hexeguitar/TGX4/hardware/img/TGX4codecModule_mount.jpg

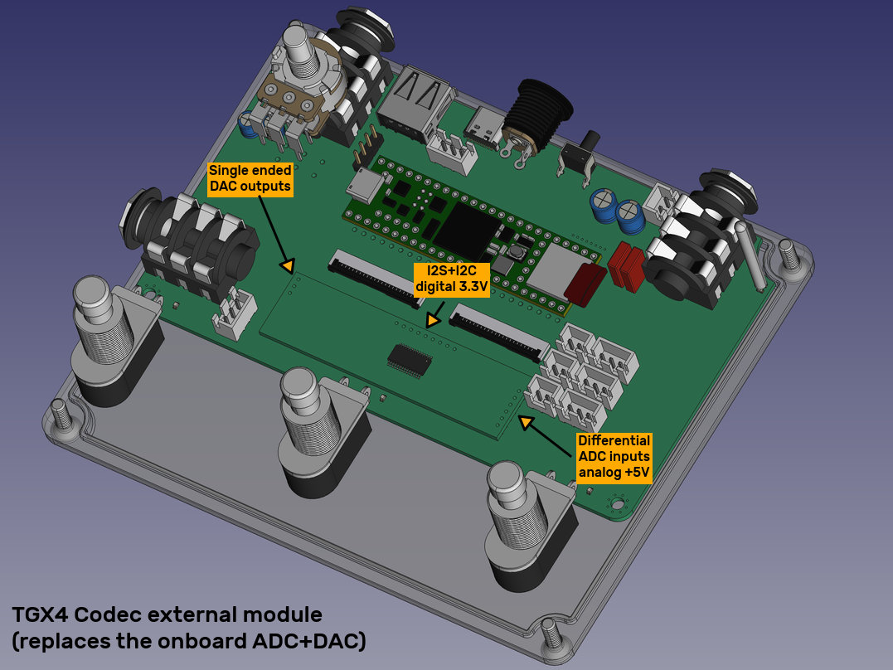
hardware/img/TGX4codecModule_mount.jpg
