hexeguitar/TGX4/hardware/KiCad_proj/MainBoard/AK5552_I2S.png

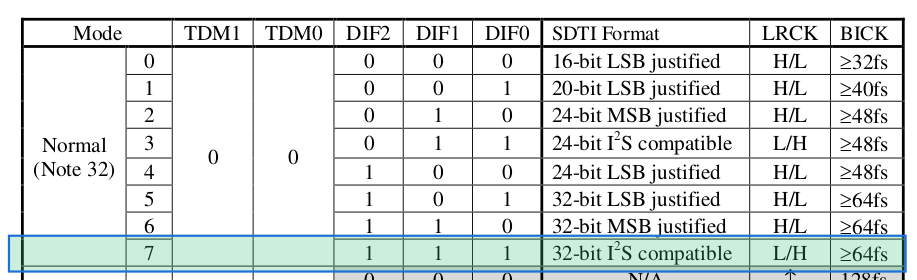
hardware/KiCad_proj/MainBoard/AK5552_I2S.png
