hexeguitar/TGX4/hardware/KiCad_proj/FrontPanel/TGX4_Panel.kicad_sch

## KiCad design hardware/KiCad_proj/FrontPanel/TGX4_Panel.kicad_sch (2024-12-13)

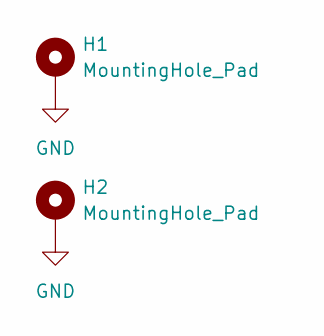
[picture p39: schematic TGX4_Panel.kicad_sch]

Parts:
H1, H2: MountingHole_Pad; MountingHole_3.2mm_M3_DIN965_Pad

Connections:
GND: H1.1, H2.1
