hexeguitar/TGX4/hardware/KiCad_proj/MainBoard/ADC_sch.kicad_sch

## KiCad design hardware/KiCad_proj/MainBoard/ADC_sch.kicad_sch (2024-07-30)

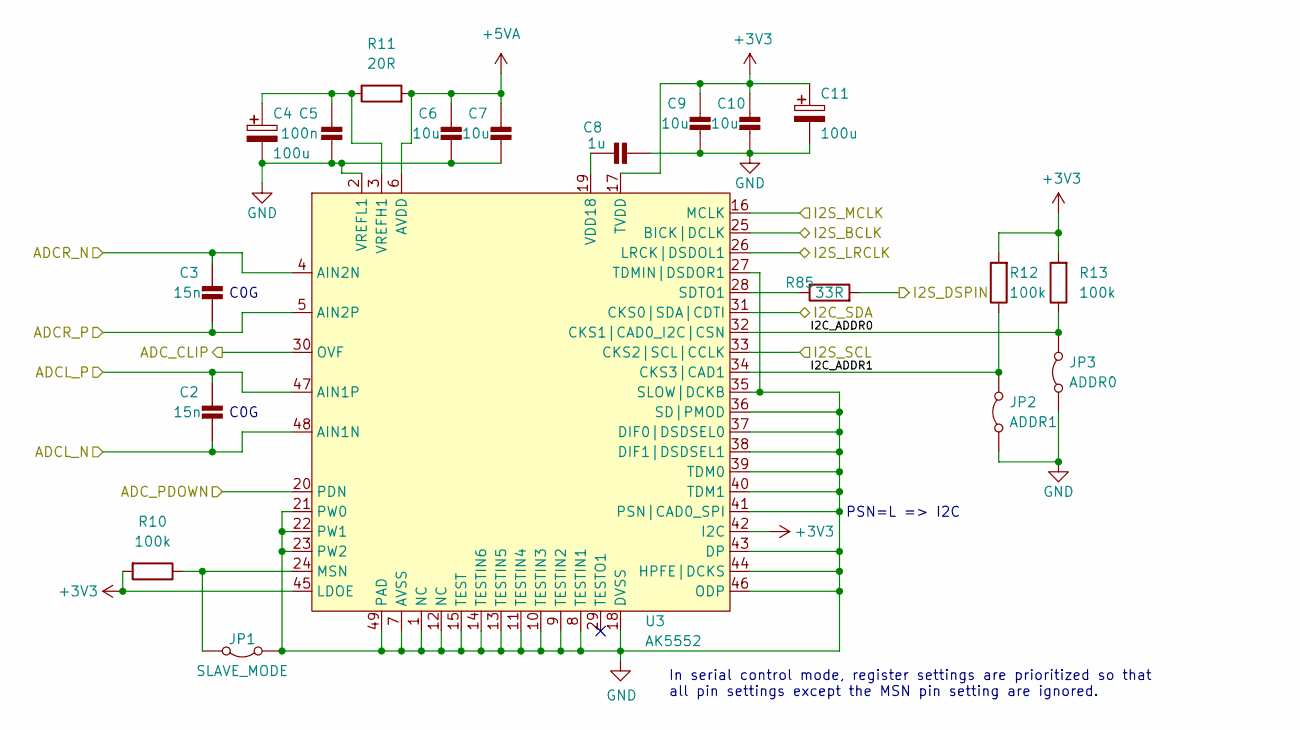
[picture p40: schematic ADC_sch.kicad_sch]

Parts:
C2, C3: 15n; Hx_C_0805_2012Metric
C4, C11: 100u; CP_EIA-6032-28_Kemet-C
C5: 100n; Hx_C_0805_2012Metric
C6, C7, C9, C10: 10u; Hx_C_0805_2012Metric
C8: 1u; Hx_C_0805_2012Metric
JP1: SLAVE_MODE; PCB_jumper_2_closed
JP2: ADDR1; PCB_jumper_2_closed
JP3: ADDR0; PCB_jumper_2_closed
R10, R12, R13: 100k; Hx_R_0805_2012Metric
R11: 20R; Hx_R_0805_2012Metric
R85: 33R; Hx_R_0805_2012Metric
U3: AK5552; QFN-48-1EP_7x7mm_P0.5mm_EP5.15x5.15mm

Connections:
+3V3: C9.1, C10.1, C11.1, R10.2, R12.2, R13.2, U3.17 (TVDD), U3.42 (I2C), U3.45 (LDOE)
+5VA: C6.1, C7.1, R11.2, U3.6 (AVDD)
ADCL_N: C2.2, U3.48 (AIN1N)
ADCL_P: C2.1, U3.47 (AIN1P)
ADCR_N: C3.1, U3.4 (AIN2N)
ADCR_P: C3.2, U3.5 (AIN2P)
ADC_CLIP: U3.30 (OVF)
ADC_PDOWN: U3.20 (PDN)
GND: C4.2, C5.2, C6.2, C7.2, C8.2, C9.2, C10.2, C11.2, JP1.1 (A), JP2.1 (A), JP3.1 (A), U3.1 (NC), U3.2 (VREFL1), U3.7 (AVSS), U3.8 (TESTIN1), U3.9 (TESTIN2), U3.10 (TESTIN3), U3.11 (TESTIN4), U3.12 (NC), U3.13 (TESTIN5), U3.14 (TESTIN6), U3.15 (TEST), U3.18 (DVSS), U3.21 (PW0), U3.22 (PW1), U3.23 (PW2), U3.27 (TDMIN|DSDOR1), U3.35 (SLOW|DCKB), U3.36 (SD|PMOD), U3.37 (DIF0|DSDSEL0), U3.38 (DIF1|DSDSEL1), U3.39 (TDM0), U3.40 (TDM1), U3.41 (PSN|CAD0_SPI), U3.43 (DP), U3.44 (HPFE|DCKS), U3.46 (ODP), U3.49 (PAD)
I2C_ADDR0: JP3.2 (B), R13.1, U3.32 (CKS1|CAD0_I2C|CSN)
I2C_ADDR1: JP2.2 (B), R12.1, U3.34 (CKS3|CAD1)
I2C_SDA: U3.31 (CKS0|SDA|CDTI)
I2S_BCLK: U3.25 (BICK|DCLK)
I2S_DSPIN: R85.2
I2S_LRCLK: U3.26 (LRCK|DSDOL1)
I2S_MCLK: U3.16 (MCLK)
I2S_SCL: U3.33 (CKS2|SCL|CCLK)
unnamed: C4.1, C5.1, R11.1, U3.3 (VREFH1)
unnamed: C8.1, U3.19 (VDD18)
unnamed: JP1.2 (B), R10.1, U3.24 (MSN)
unnamed: R85.1, U3.28 (SDTO1)

Notes on the sheet:
C0G
PSN=L => I2C
In serial control mode, register settings are prioritized so that all pin settings except the MSN pin setting are ignored.
