hexeguitar/TGX4/hardware/KiCad_proj/MainBoard/Audio_Input.kicad_sch

## KiCad design hardware/KiCad_proj/MainBoard/Audio_Input.kicad_sch (2024-07-30)

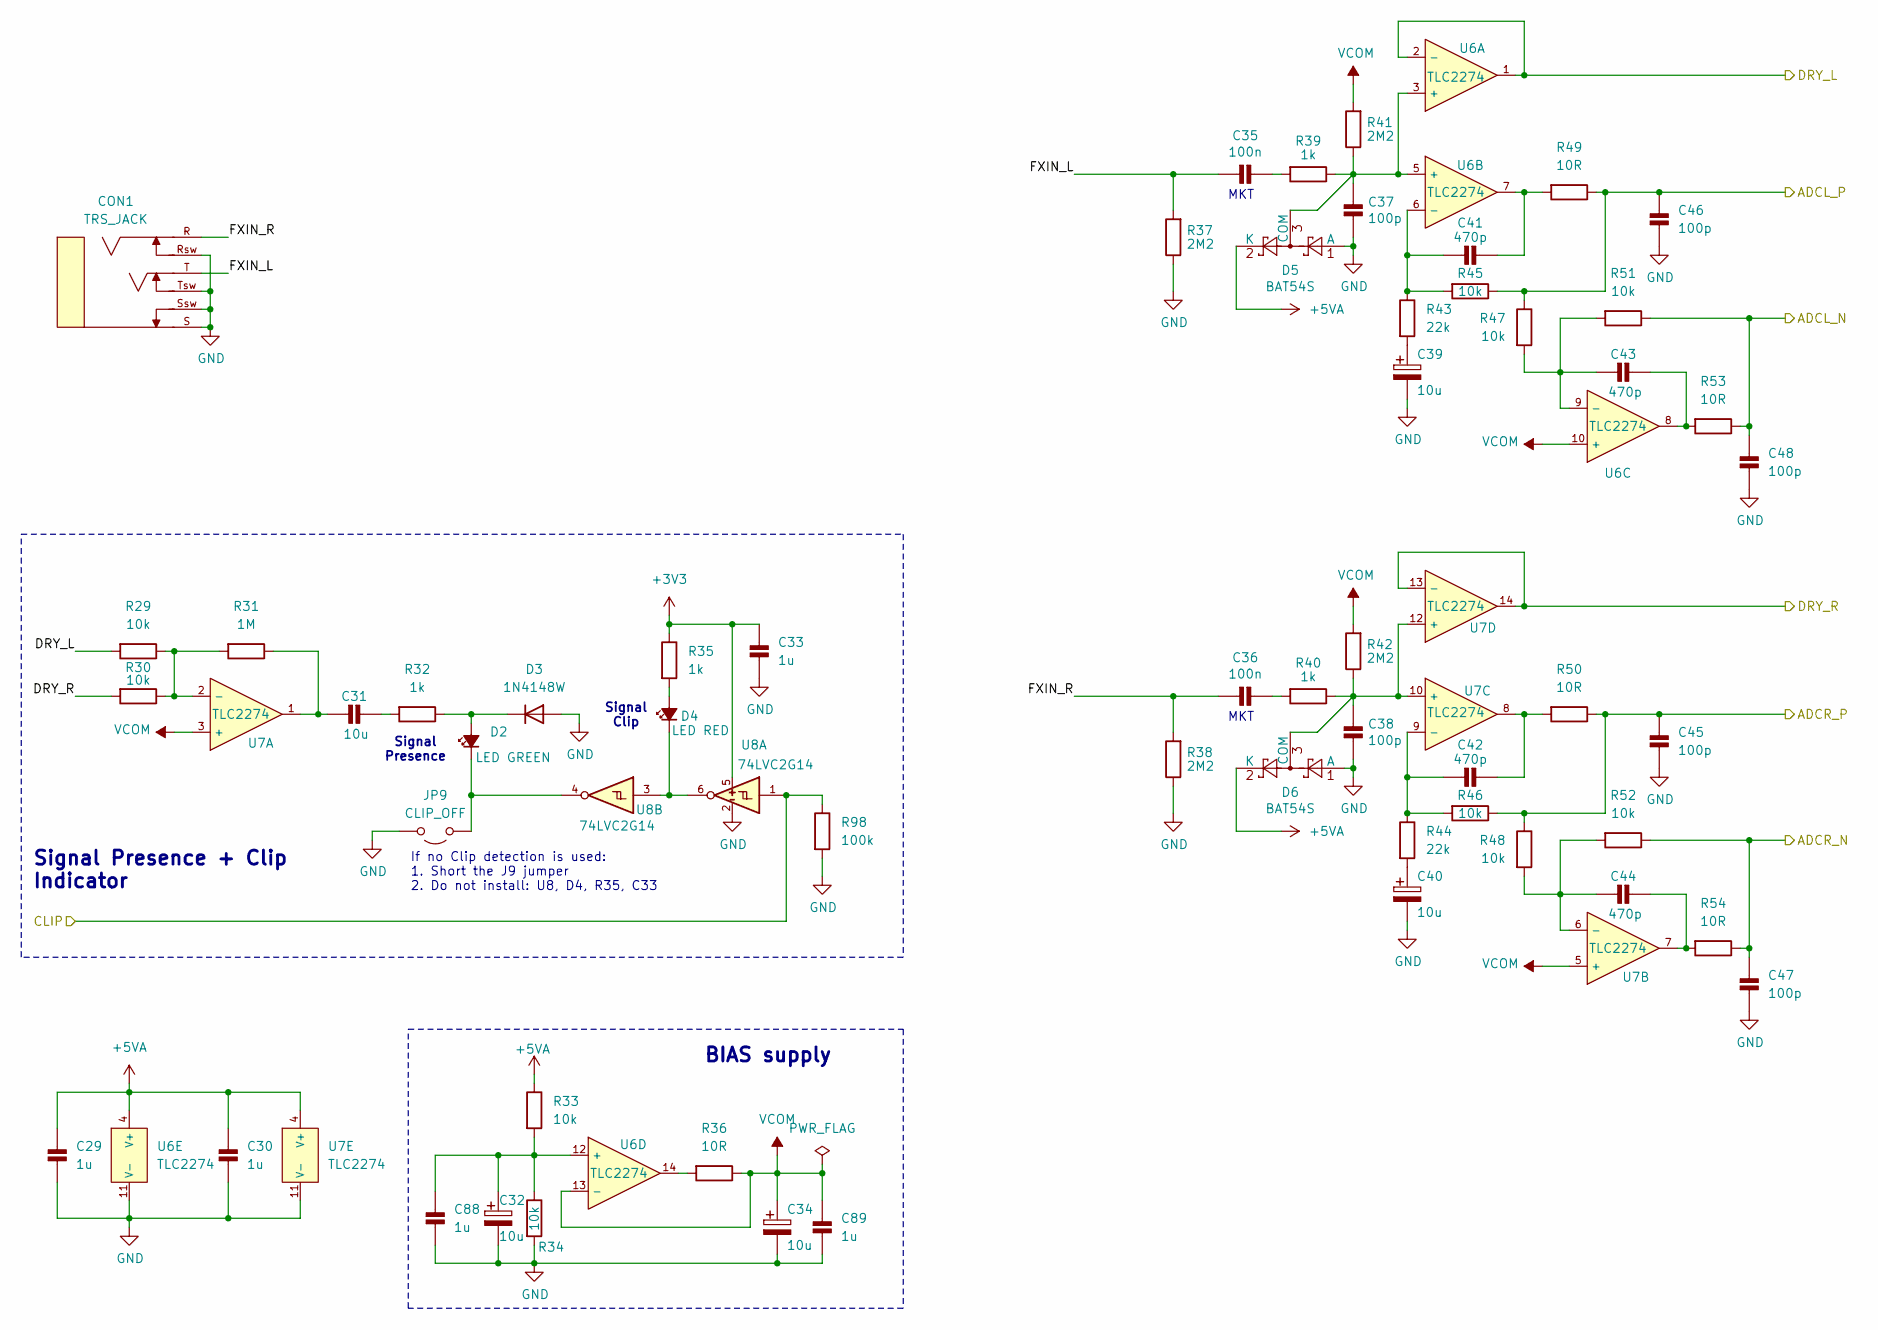
[picture p41: schematic Audio_Input.kicad_sch]

Parts:
C29, C30, C33, C88, C89: 1u; Hx_C_0805_2012Metric
C31: 10u; Hx_C_0805_2012Metric
C32, C34, C39, C40: 10u; CP_EIA-3216-18_Kemet-A
C35, C36: 100n; C_Rect_L7.0mm_W2.5mm_P5.00mm
C37, C38, C45, C46, C47, C48: 100p; Hx_C_0805_2012Metric
C41, C42, C43, C44: 470p; Hx_C_0805_2012Metric
CON1: TRS_JACK; NMJ6HCD2_TRSjack_smallPads
D2: LED GREEN; LED_0603_1608Metric
D3: 1N4148W; D_SOD-123
D4: LED RED; LED_0603_1608Metric
D5, D6: BAT54S; SOT-23
JP9: CLIP_OFF; PCB_jumper_2
R29, R30, R33, R34, R45, R46, R47, R48, R51, R52: 10k; Hx_R_0805_2012Metric
R31: 1M; Hx_R_0805_2012Metric
R32, R35, R39, R40: 1k; Hx_R_0805_2012Metric
R36, R49, R50, R53, R54: 10R; Hx_R_0805_2012Metric
R37, R38, R41, R42: 2M2; Hx_R_0805_2012Metric
R43, R44: 22k; Hx_R_0805_2012Metric
R98: 100k; Hx_R_0805_2012Metric
U6, U7: TLC2274; SO-14_3.9x8.65mm_P1.27mm
U8: 74LVC2G14; SOT-363_SC-70-6

Connections:
+3V3: C33.1, R35.1, U8.5
+5VA: C29.1, C30.1, D5.2 (K), D6.2 (K), R33.1, U6.4 (V+), U7.4 (V+)
ADCL_N: C48.1, R51.1, R53.1
ADCL_P: C46.1, R45.1, R47.1, R49.1
ADCR_N: C47.1, R52.1, R54.1
ADCR_P: C45.1, R46.1, R48.1, R50.1
CLIP: R98.1, U8.1
DRY_L: R29.2, U6.1, U6.2 (-)
DRY_R: R30.2, U7.13 (-), U7.14
FXIN_L: C35.2, CON1.T, R37.2
FXIN_R: C36.2, CON1.R, R38.2
GND: C29.2, C30.2, C32.2, C33.2, C34.2, C37.2, C38.2, C39.2, C40.2, C45.2, C46.2, C47.2, C48.2, C88.2, C89.2, CON1.Rsw, CON1.S, CON1.Ssw, CON1.Tsw, D3.2 (A), D5.1 (A), D6.1 (A), JP9.1 (A), R34.2, R37.1, R38.1, R98.2, U6.11 (V-), U7.11 (V-), U8.2
unnamed: C31.1, R32.2
unnamed: C31.2, R31.1, U7.1
unnamed: C32.1, C88.1, R33.2, R34.1, U6.12 (+)
unnamed: C35.1, R39.2
unnamed: C36.1, R40.2
unnamed: C37.1, D5.3 (COM), R39.1, R41.1, U6.3 (+), U6.5 (+)
unnamed: C38.1, D6.3 (COM), R40.1, R42.1, U7.10 (+), U7.12 (+)
unnamed: C39.1, R43.2
unnamed: C40.1, R44.2
unnamed: C41.1, R49.2, U6.7
unnamed: C41.2, R43.1, R45.2, U6.6 (-)
unnamed: C42.1, R50.2, U7.8
unnamed: C42.2, R44.1, R46.2, U7.9 (-)
unnamed: C43.1, R53.2, U6.8
unnamed: C43.2, R47.2, R51.2, U6.9 (-)
unnamed: C44.1, R54.2, U7.7
unnamed: C44.2, R48.2, R52.2, U7.6 (-)
unnamed: D2.1 (K), JP9.2 (B), U8.4
unnamed: D2.2 (A), D3.1 (K), R32.1
unnamed: D4.1 (K), U8.3, U8.6
unnamed: D4.2 (A), R35.2
unnamed: R29.1, R30.1, R31.2, U7.2 (-)
unnamed: R36.2, U6.14
VCOM: C34.1, C89.1, R36.1, R41.2, R42.2, U6.10 (+), U6.13 (-), U7.3 (+), U7.5 (+)

Notes on the sheet:
MKT
If no Clip detection is used: 1. Short the J9 jumper 2. Do not install: U8, D4, R35, C33
Signal Presence + Clip Indicator
BIAS supply
Signal Presence
Signal Clip
