hexeguitar/TGX4/hardware/KiCad_proj/MainBoard/Audio_Output.kicad_sch

## KiCad design hardware/KiCad_proj/MainBoard/Audio_Output.kicad_sch (2024-07-30)

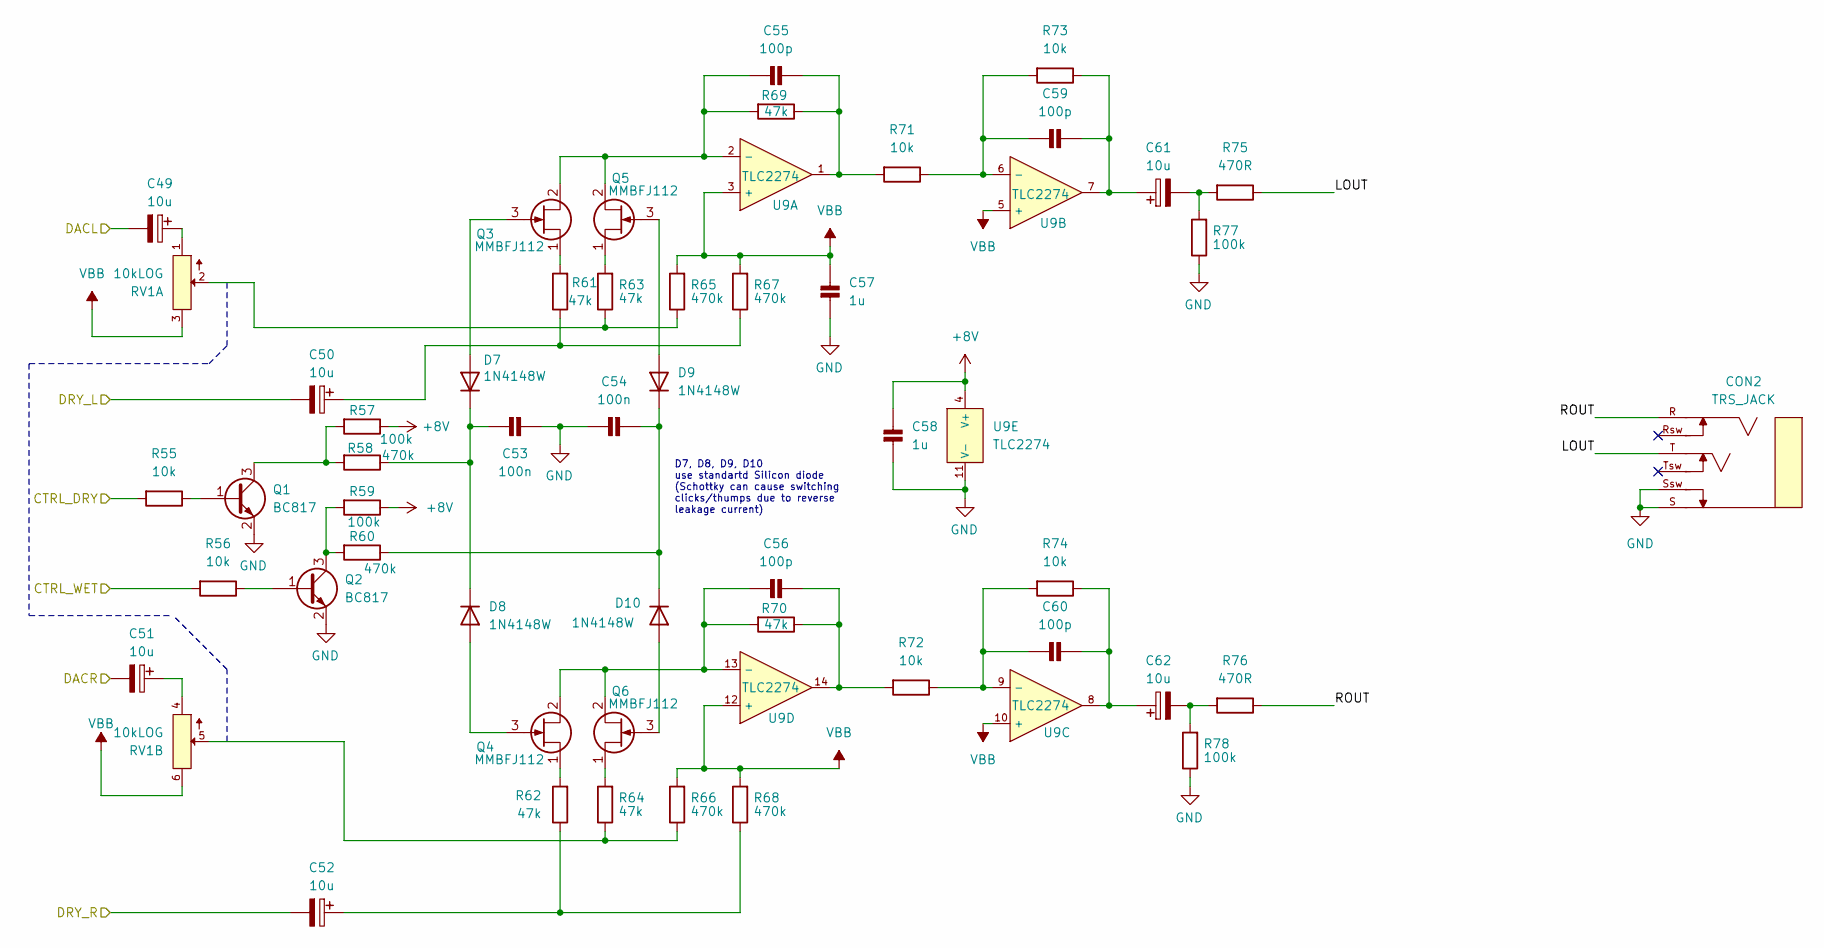
[picture p42: schematic Audio_Output.kicad_sch]

Parts:
C49, C50, C51, C52, C61, C62: 10u; CP_EIA-3216-18_Kemet-A
C53, C54: 100n; Hx_C_0805_2012Metric
C55, C56, C59, C60: 100p; Hx_C_0805_2012Metric
C57, C58: 1u; Hx_C_0805_2012Metric
CON2: TRS_JACK; NMJ6HCD2_TRSjack_smallPads
D7, D8, D9, D10: 1N4148W; D_SOD-123
Q1, Q2: BC817; SOT-23
Q3, Q4, Q5, Q6: MMBFJ112; SOT-23
R55, R56, R71, R72, R73, R74: 10k; Hx_R_0805_2012Metric
R57, R59, R77, R78: 100k; Hx_R_0805_2012Metric
R58, R60, R65, R66, R67, R68: 470k; Hx_R_0805_2012Metric
R61, R62, R63, R64, R69, R70: 47k; Hx_R_0805_2012Metric
R75, R76: 470R; Hx_R_0805_2012Metric
RV1: 10kLOG; ALPHA_DUALPOT_16mm
U9: TLC2274; SO-14_3.9x8.65mm_P1.27mm

Connections:
+8V: C58.1, R57.1, R59.1, U9.4 (V+)
CTRL_DRY: R55.2
CTRL_WET: R56.2
DACL: C49.2
DACR: C51.2
DRY_L: C50.2
DRY_R: C52.2
GND: C53.1, C54.2, C57.2, C58.2, CON2.S, CON2.Ssw, Q1.2 (E), Q2.2 (E), R77.1, R78.1, U9.11 (V-)
LOUT: CON2.T, R75.1
unnamed: C49.1, RV1.1
unnamed: C50.1, R61.1, R67.1
unnamed: C51.1, RV1.4
unnamed: C52.1, R62.1, R68.1
unnamed: C53.2, D7.1 (K), D8.1 (K), R58.1
unnamed: C54.1, D9.1 (K), D10.1 (K), R60.1
unnamed: C55.1, Q3.2 (S), Q5.2 (S), R69.2, U9.2 (-)
unnamed: C55.2, R69.1, R71.2, U9.1
unnamed: C56.1, Q4.2 (S), Q6.2 (S), R70.2, U9.13 (-)
unnamed: C56.2, R70.1, R72.2, U9.14
unnamed: C59.1, R71.1, R73.2, U9.6 (-)
unnamed: C59.2, C61.1, R73.1, U9.7
unnamed: C60.1, R72.1, R74.2, U9.9 (-)
unnamed: C60.2, C62.1, R74.1, U9.8
unnamed: C61.2, R75.2, R77.2
unnamed: C62.2, R76.2, R78.2
unnamed: D7.2 (A), Q3.3 (G)
unnamed: D8.2 (A), Q4.3 (G)
unnamed: D9.2 (A), Q5.3 (G)
unnamed: D10.2 (A), Q6.3 (G)
unnamed: Q1.1 (B), R55.1
unnamed: Q1.3 (C), R57.2, R58.2
unnamed: Q2.1 (B), R56.1
unnamed: Q2.3 (C), R59.2, R60.2
unnamed: Q3.1 (D), R61.2
unnamed: Q4.1 (D), R62.2
unnamed: Q5.1 (D), R63.2
unnamed: Q6.1 (D), R64.2
unnamed: R63.1, R65.1, RV1.2
unnamed: R64.1, R66.1, RV1.5
ROUT: CON2.R, R76.1
VBB: C57.1, R65.2, R66.2, R67.2, R68.2, RV1.3, RV1.6, U9.3 (+), U9.5 (+), U9.10 (+), U9.12 (+)

Notes on the sheet:
D7, D8, D9, D10 use standartd Silicon diode (Schottky can cause switching clicks/thumps due to reverse leakage current)
