hexeguitar/TGX4/hardware/KiCad_proj/MainBoard/DAC.kicad_sch

## KiCad design hardware/KiCad_proj/MainBoard/DAC.kicad_sch (2024-07-30)

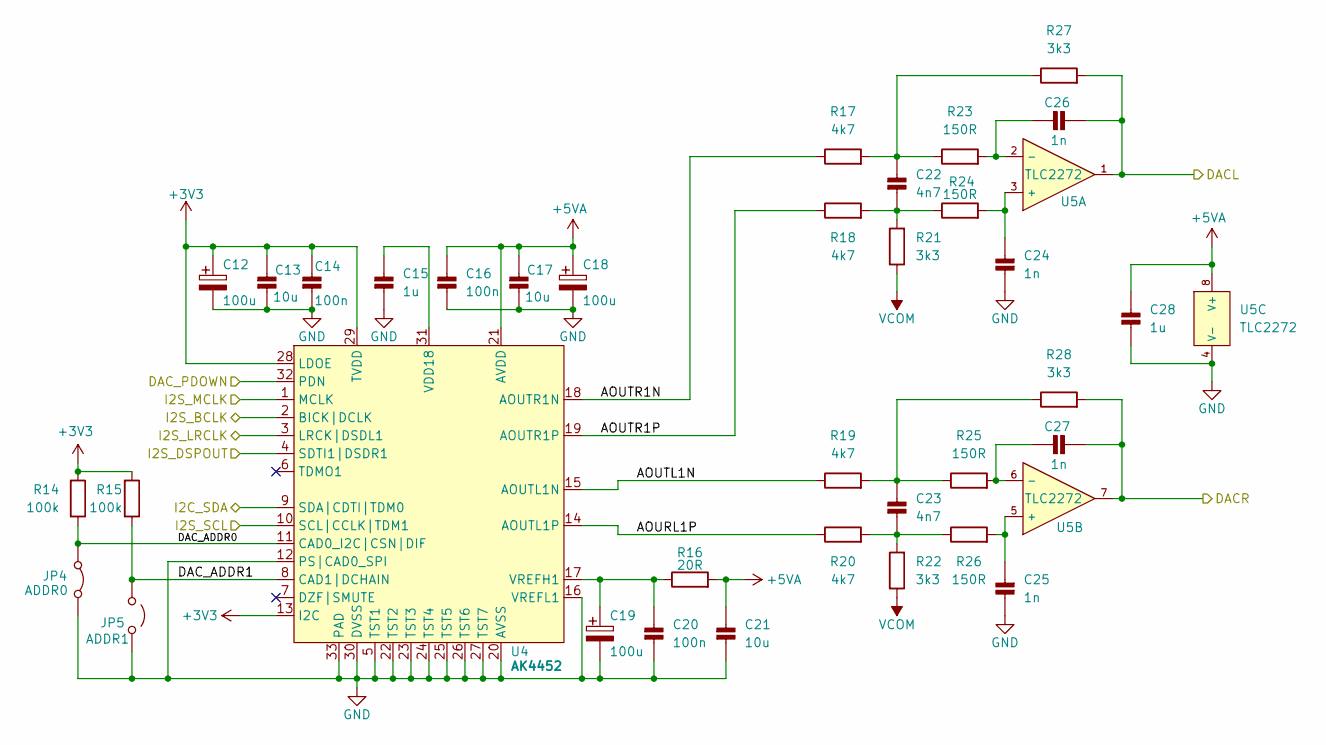
[picture p43: schematic DAC.kicad_sch]

Parts:
C12, C18, C19: 100u; CP_EIA-6032-28_Kemet-C
C13, C17, C21: 10u; Hx_C_0805_2012Metric
C14, C16, C20: 100n; Hx_C_0805_2012Metric
C15, C28: 1u; Hx_C_0805_2012Metric
C22, C23: 4n7; Hx_C_0805_2012Metric
C24, C25, C26, C27: 1n; Hx_C_0805_2012Metric
JP4: ADDR0; PCB_jumper_2_closed
JP5: ADDR1; PCB_jumper_2
R14, R15: 100k; Hx_R_0805_2012Metric
R16: 20R; Hx_R_0805_2012Metric
R17, R18, R19, R20: 4k7; Hx_R_0805_2012Metric
R21, R22, R27, R28: 3k3; Hx_R_0805_2012Metric
R23, R24, R25, R26: 150R; Hx_R_0805_2012Metric
U4: AK4452; QFN-32-1EP_5x5mm_P0.5mm_EP3.1x3.1mm
U5: TLC2272; SO-8_3.9x4.9mm_P1.27mm

Connections:
+3V3: C12.1, C13.1, C14.1, R14.2, R15.2, U4.13 (I2C), U4.28 (LDOE), U4.29 (TVDD)
+5VA: C16.1, C17.1, C18.1, C21.1, C28.1, R16.2, U4.21 (AVDD), U5.8 (V+)
AOURL1P: R20.1, U4.14 (AOUTL1P)
AOUTL1N: R19.1, U4.15 (AOUTL1N)
AOUTR1N: R17.1, U4.18 (AOUTR1N)
AOUTR1P: R18.1, U4.19 (AOUTR1P)
DACL: C26.2, R27.2, U5.1
DACR: C27.2, R28.2, U5.7
DAC_ADDR0: JP4.2 (B), R14.1, U4.11 (CAD0_I2C|CSN|DIF)
DAC_ADDR1: JP5.2 (B), R15.1, U4.8 (CAD1|DCHAIN)
DAC_PDOWN: U4.32 (PDN)
GND: C12.2, C13.2, C14.2, C15.2, C16.2, C17.2, C18.2, C19.2, C20.2, C21.2, C24.1, C25.1, C28.2, JP4.1 (A), JP5.1 (A), U4.5 (TST1), U4.12 (PS|CAD0_SPI), U4.16 (VREFL1), U4.20 (AVSS), U4.22 (TST2), U4.23 (TST3), U4.24 (TST4), U4.25 (TST5), U4.26 (TST6), U4.27 (TST7), U4.30 (DVSS), U4.33 (PAD), U5.4 (V-)
I2C_SDA: U4.9 (SDA|CDTI|TDM0)
I2S_BCLK: U4.2 (BICK|DCLK)
I2S_DSPOUT: U4.4 (SDTI1|DSDR1)
I2S_LRCLK: U4.3 (LRCK|DSDL1)
I2S_MCLK: U4.1 (MCLK)
I2S_SCL: U4.10 (SCL|CCLK|TDM1)
unnamed: C15.1, U4.31 (VDD18)
unnamed: C19.1, C20.1, R16.1, U4.17 (VREFH1)
unnamed: C22.1, R17.2, R23.1, R27.1
unnamed: C22.2, R18.2, R21.2, R24.1
unnamed: C23.1, R19.2, R25.1, R28.1
unnamed: C23.2, R20.2, R22.2, R26.1
unnamed: C24.2, R24.2, U5.3 (+)
unnamed: C25.2, R26.2, U5.5 (+)
unnamed: C26.1, R23.2, U5.2 (-)
unnamed: C27.1, R25.2, U5.6 (-)
VCOM: R21.1, R22.1
