hexeguitar/TGX4/hardware/KiCad_proj/MainBoard/Power.kicad_sch

## KiCad design hardware/KiCad_proj/MainBoard/Power.kicad_sch (2024-07-30)

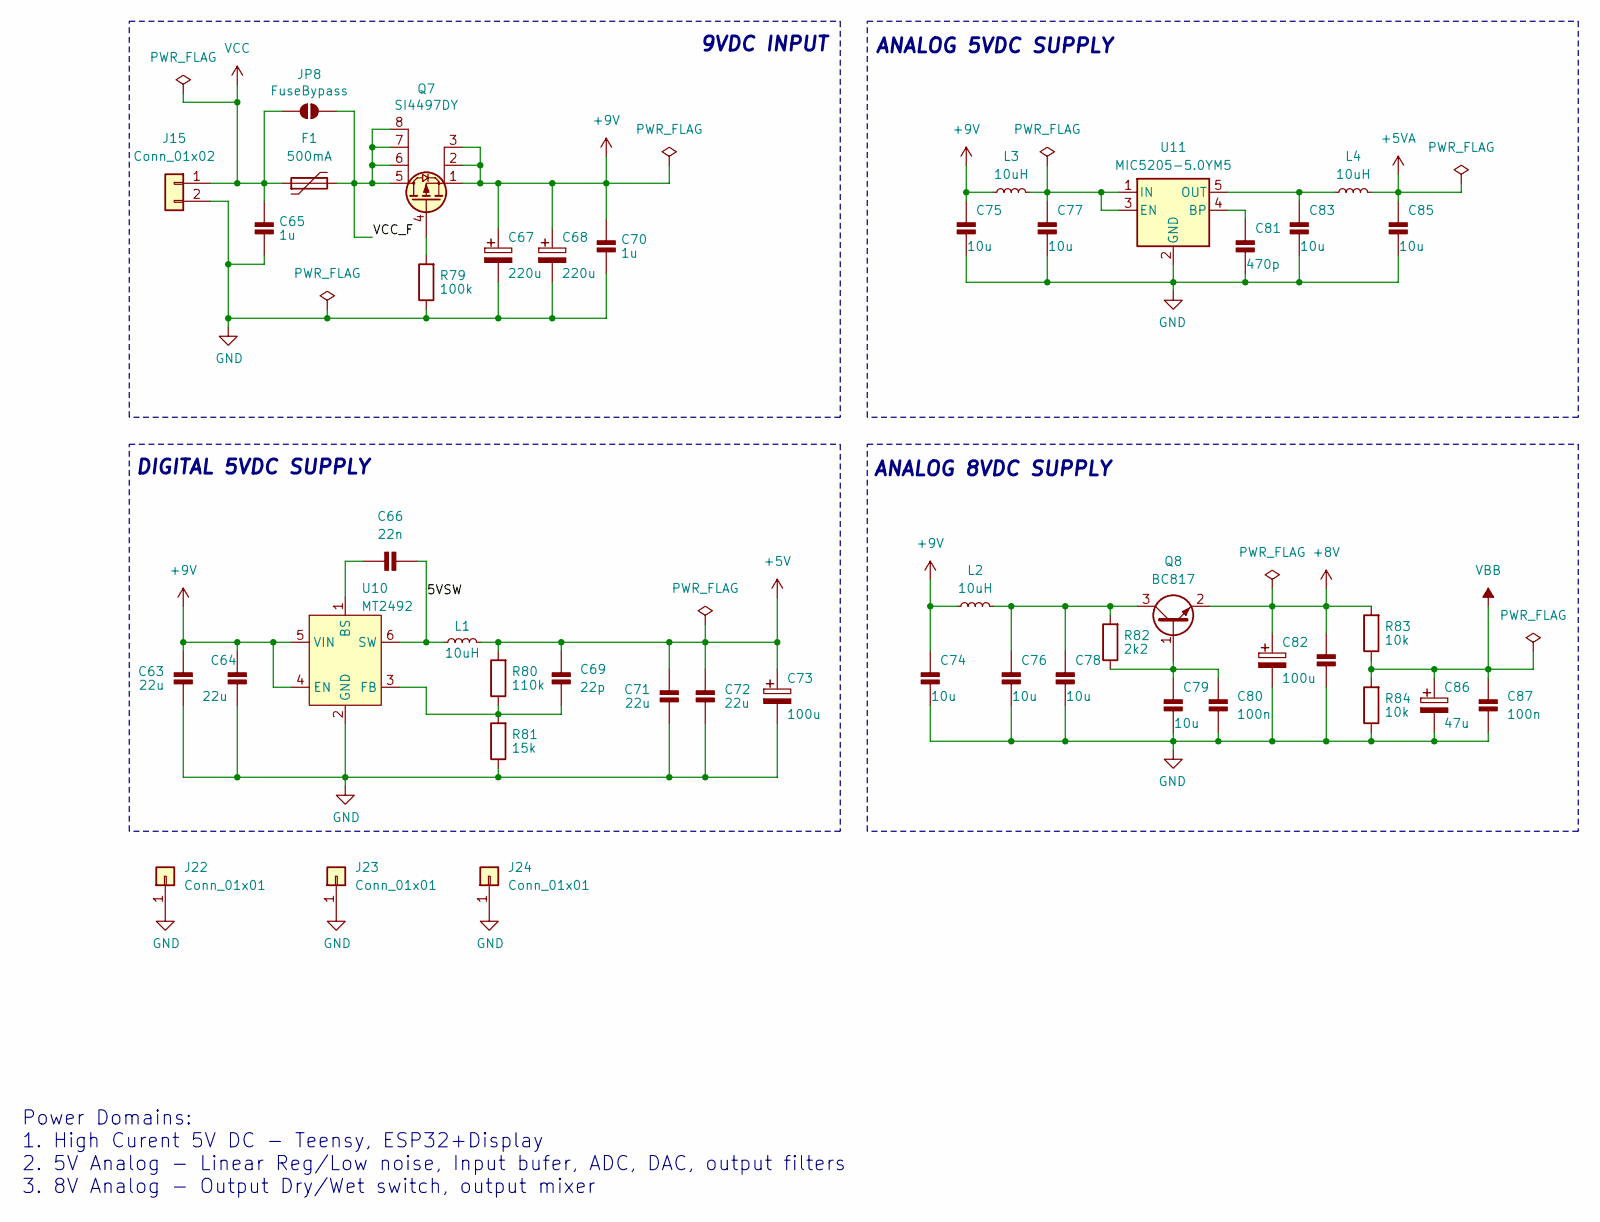
[picture p44: schematic Power.kicad_sch]

Parts:
C63, C64, C71, C72: 22u; Hx_C_0805_2012Metric
C65, C70: 1u; Hx_C_0805_2012Metric
C66: 22n; Hx_C_0805_2012Metric
C67, C68: 220u; CP_Radial_D6.3mm_P2.50mm
C69: 22p; Hx_C_0805_2012Metric
C73: 100u; CP_EIA-6032-28_Kemet-C
C74, C75, C76, C77, C78, C79, C83, C85: 10u; Hx_C_0805_2012Metric
C80, C84, C87: 100n; Hx_C_0805_2012Metric
C81: 470p; Hx_C_0805_2012Metric
C82: 100u; CP_Radial_D5.0mm_P2.00mm
C86: 47u; CP_Radial_D5.0mm_P2.00mm
F1: 500mA; Fuse_1812_4532Metric
J15: Conn_01x02; JST_XA_B02B-XASK-1_1x02_P2.50mm_Vertical
J22, J23, J24: Conn_01x01; PinHeader_1x01_P2.00mm_Vertical
JP8: FuseBypass; PCB_jumper_2
L1: 10uH; L_Changjiang_FNR5020S
L2, L3, L4: 10uH; Hx_L_0805_2012Metric
Q7: SI4497DY; SO-8_3.9x4.9mm_P1.27mm
Q8: BC817; SOT-23
R79: 100k; Hx_R_0805_2012Metric
R80: 110k; Hx_R_0805_2012Metric
R81: 15k; Hx_R_0805_2012Metric
R82: 2k2; Hx_R_0805_2012Metric
R83, R84: 10k; Hx_R_0805_2012Metric
U10: MT2492; SOT-23-6
U11: MIC5205-5.0YM5; SOT-23-5

Connections:
5VSW: C66.2, L1.2, U10.6 (SW)
+5V: C69.1, C71.1, C72.1, C73.1, L1.1, R80.2
+5VA: C85.1, L4.2
+8V: C82.1, C84.1, Q8.2 (E), R83.2
+9V: C63.1, C64.1, C67.1, C68.1, C70.1, C74.1, C75.1, L2.1, L3.1, Q7.1 (S), Q7.2 (S), Q7.3 (S), U10.4 (EN), U10.5 (VIN)
GND: C63.2, C64.2, C65.2, C67.2, C68.2, C70.2, C71.2, C72.2, C73.2, C74.2, C75.2, C76.2, C77.2, C78.2, C79.2, C80.2, C81.2, C82.2, C83.2, C84.2, C85.2, C86.2, C87.2, J15.2, J22.1, J23.1, J24.1, R79.1, R81.1, R84.1, U10.2 (GND), U11.2 (GND)
unnamed: C66.1, U10.1 (BS)
unnamed: C69.2, R80.1, R81.2, U10.3 (FB)
unnamed: C76.1, C78.1, L2.2, Q8.3 (C), R82.2
unnamed: C77.1, L3.2, U11.1 (IN), U11.3 (EN)
unnamed: C79.1, C80.1, Q8.1 (B), R82.1
unnamed: C81.1, U11.4 (BP)
unnamed: C83.1, L4.1, U11.5 (OUT)
unnamed: Q7.4 (G), R79.2
VBB: C86.1, C87.1, R83.1, R84.2
VCC: C65.1, F1.1, J15.1, JP8.1 (A)
VCC_F: F1.2, JP8.2 (B), Q7.5 (D), Q7.6 (D), Q7.7 (D), Q7.8 (D)

Notes on the sheet:
9VDC INPUT
ANALOG 8VDC SUPPLY
ANALOG 5VDC SUPPLY
Power Domains: 1. High Curent 5V DC - Teensy, ESP32+Display 2. 5V Analog - Linear Reg/Low noise, Input bufer, ADC, DAC, output filters 3. 8V Analog - Output Dry/Wet switch, output mixer
DIGITAL 5VDC SUPPLY
