hexeguitar/TGX4/hardware/KiCad_proj/MainBoard/TGX4.kicad_sch

## KiCad design hardware/KiCad_proj/MainBoard/TGX4.kicad_sch (2024-07-30)

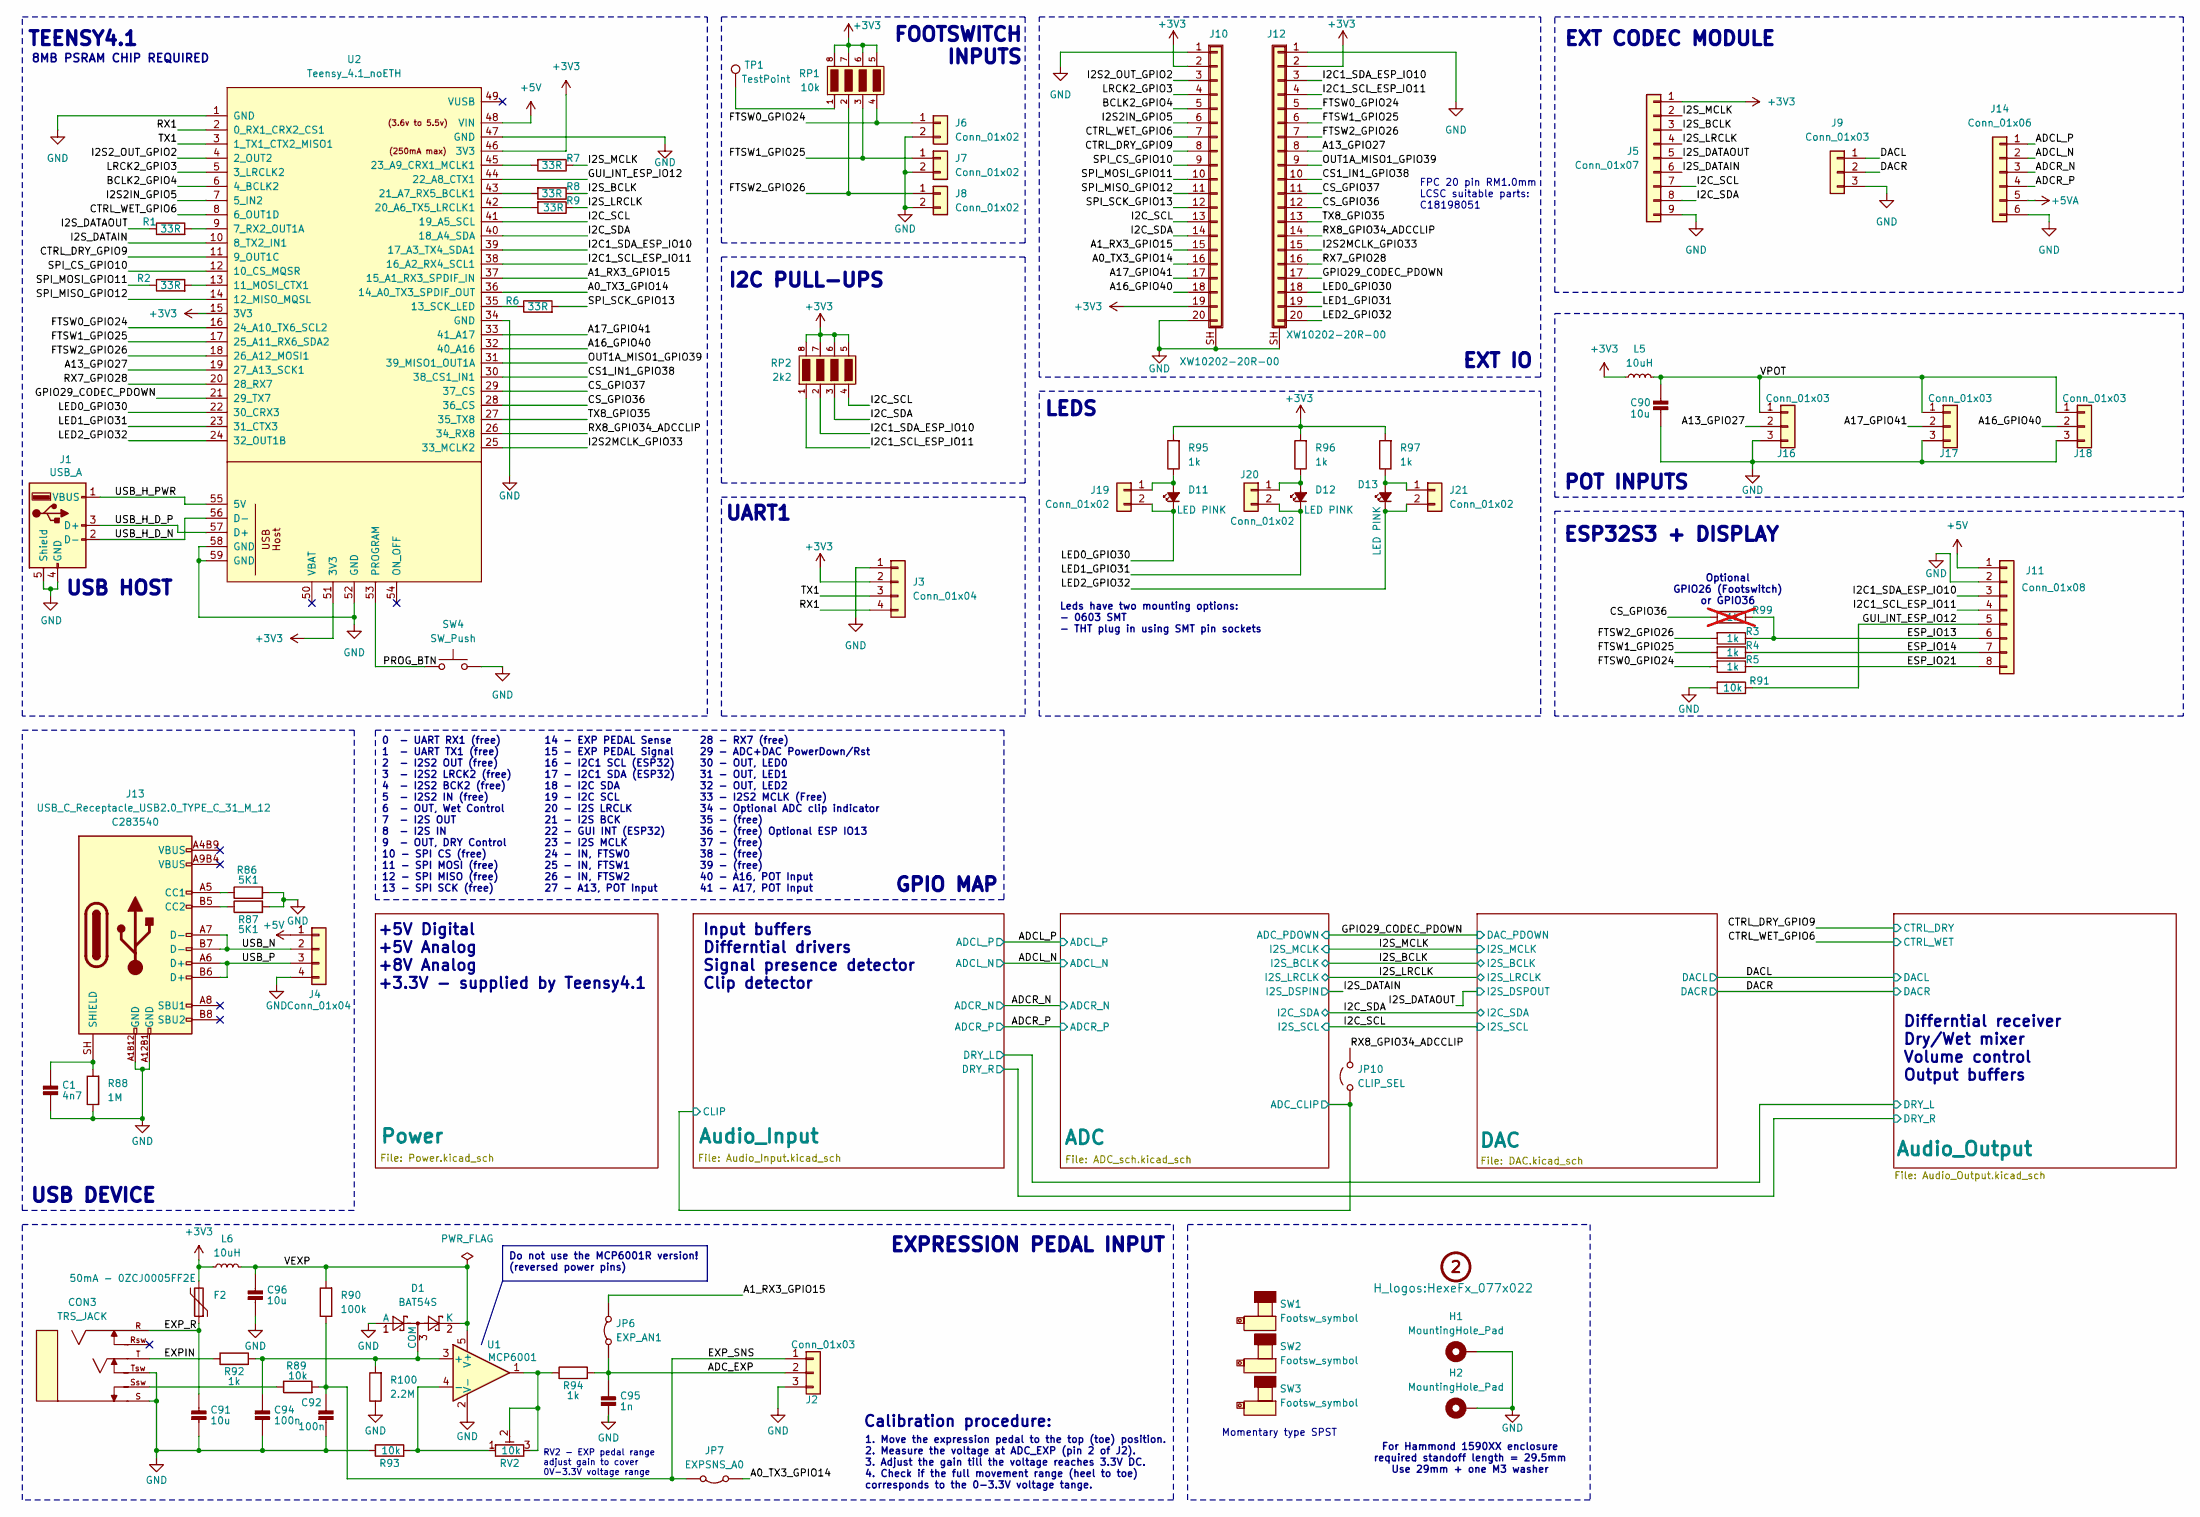
[picture p45: schematic TGX4.kicad_sch]

Parts:
C1: 4n7; Hx_C_0805_2012Metric
C90, C91, C96: 10u; Hx_C_0805_2012Metric
C92, C94: 100n; Hx_C_0805_2012Metric
C95: 1n; Hx_C_0805_2012Metric
CON3: TRS_JACK; NMJ6HCD2_TRSjack_smallPads
D1: BAT54S; SOT-23
D11, D12, D13: LED PINK; LED_0603_1608Metric
F2: 50mA - 0ZCJ0005FF2E; Fuse_1206_3216Metric
H1, H2: MountingHole_Pad; MountingHole_3.2mm_M3_Pad_Via
J1: USB_A; USB_A_Molex_67643_Horizontal
J2, J16, J17, J18: Conn_01x03; JST_XA_B03B-XASK-1_1x03_P2.50mm_Vertical
J3: Conn_01x04; PinHeader_1x04_P2.54mm_Vertical
J4: Conn_01x04; JST_XA_B04B-XASK-1_1x04_P2.50mm_Vertical
J5: Conn_01x07; PinSocket_1x09_P2.00mm_Vertical
J6, J7, J8: Conn_01x02; JST_XA_B02B-XASK-1_1x02_P2.50mm_Vertical
J9: Conn_01x03; PinSocket_1x03_P2.00mm_Vertical
J10, J12: XW10202-20R-00; HCTL_XW10202-20R-00 _1x20-1MP_P1.00mm_Horizontal
J11: Conn_01x08; Molex_PicoBlade_53047-0810_1x08_P1.25mm_Vertical
J13: USB_C_Receptacle_USB2.0_TYPE_C_31_M_12; USB_C_TYPE-C-31-M-12; LCSC C283540
J14: Conn_01x06; PinSocket_1x06_P2.00mm_Vertical
J19, J20, J21: Conn_01x02; PinSocket_1x02_P2.54mm_Vertical_SMD_Pin1Left
JP6: EXP_AN1; PCB_jumper_2_closed
JP7: EXPSNS_A0; PCB_jumper_2_closed
JP10: CLIP_SEL; PCB_jumper_2
L5, L6: 10uH; Hx_L_0805_2012Metric
R1, R2, R6, R7, R8, R9: 33R; Hx_R_0805_2012Metric
R3, R4, R5, R92, R94, R95, R96, R97: 1k; Hx_R_0805_2012Metric
R86, R87: 5K1; Hx_R_0805_2012Metric
R88: 1M; Hx_R_0805_2012Metric
R89, R91, R93: 10k; Hx_R_0805_2012Metric
R90: 100k; Hx_R_0805_2012Metric
R99: 1k; Hx_R_0805_2012Metric; not fitted
R100: 2.2M; Hx_R_0805_2012Metric
RP1: 10k; R_Array_Convex_4x0603
RP2: 2k2; R_Array_Convex_4x0603
RV2: 10k; Trimpot_SMD_mini
S2: Detail2; HexeFx_077x022
SW1, SW2, SW3: Footsw_symbol; FootswitchTopView
SW4: SW_Push; SW_Tactile_SPST_Angled_PTS645Vx83-2LFS
TP1: TestPoint; TestPoint_Pad_D1.0mm
U1: MCP6001; SOT-23-5
U2: Teensy_4.1_noETH; Teensy41_noETH

Connections:
+3V3: F2.2, J3.2, J5.1, J10.2, J10.19, J12.2, L5.2, L6.2, R95.2, R96.2, R97.2, RP1.5 (R4), RP1.6 (R3), RP1.7 (R2), RP1.8 (R1), RP2.5 (R4), RP2.6 (R3), RP2.7 (R2), RP2.8 (R1), U2.15 (3V3), U2.46 (3V3), U2.51 (3V3)
+5V: J4.1, J11.1, U2.48 (VIN)
+5VA: J14.5
A0_TX3_GPIO14: J10.16, JP7.2 (B), U2.36 (14_A0_TX3_SPDIF_OUT)
A1_RX3_GPIO15: J10.15, JP6.2 (B), U2.37 (15_A1_RX3_SPDIF_IN)
A13_GPIO27: J12.8, J16.2, U2.19 (27_A13_SCK1)
A16_GPIO40: J10.18, J18.2, U2.32 (40_A16)
A17_GPIO41: J10.17, J17.2, U2.33 (41_A17)
ADCL_N: J14.2
ADCL_P: J14.1
ADCR_N: J14.3
ADCR_P: J14.4
ADC_CLIP: JP10.1 (A)
ADC_EXP: C95.1, J2.2, JP6.1 (A), R94.2
BCLK2_GPIO4: J10.5, U2.6 (4_BCLK2)
CS1_IN1_GPIO38: J12.10, U2.30 (38_CS1_IN1)
CS_GPIO36: J12.12, R99.2, U2.28 (36_CS)
CS_GPIO37: J12.11, U2.29 (37_CS)
CTRL_DRY_GPIO9: J10.8, U2.11 (9_OUT1C)
CTRL_WET_GPIO6: J10.7, U2.8 (6_OUT1D)
DACL: J9.1
DACR: J9.2
ESP_IO13: J11.6, R3.1, R99.1
ESP_IO14: J11.7, R4.1
ESP_IO21: J11.8, R5.1
EXPIN: CON3.T, R92.1
EXP_R: C91.1, CON3.R, F2.1
EXP_SNS: C92.1, J2.1, JP7.1 (A), R89.2, R90.1
FTSW0_GPIO24: J6.1, J12.5, R5.2, RP1.4, U2.16 (24_A10_TX6_SCL2)
FTSW1_GPIO25: J7.1, J12.6, R4.2, RP1.3, U2.17 (25_A11_RX6_SDA2)
FTSW2_GPIO26: J8.1, J12.7, R3.2, RP1.2, U2.18 (26_A12_MOSI1)
GND: C1.2, C90.2, C91.2, C92.2, C94.2, C95.2, C96.2, CON3.S, CON3.Tsw, D1.1 (A), H1.1, H2.1, J1.4 (GND), J1.5 (Shield), J2.3, J3.1, J4.4, J5.9, J6.2, J7.2, J8.2, J9.3, J10.1, J10.20, J10.SH (Shield), J11.2, J12.1, J12.SH (Shield), J13.A1B12 (GND), J13.A12B1 (GND), J14.6, J16.3, J17.3, J18.3, R86.2, R87.2, R88.1, R91.2, R93.1, R100.1, SW4.2, U1.2 (V-), U2.1 (GND), U2.34 (GND), U2.47 (GND), U2.52 (GND), U2.58 (GND), U2.59 (GND)
GPIO29_CODEC_PDOWN: J12.17, U2.21 (29_TX7)
GUI_INT_ESP_IO12: J11.5, R91.1, U2.44 (22_A8_CTX1)
I2C1_SCL_ESP_IO11: J11.4, J12.4, RP2.1, U2.38 (16_A2_RX4_SCL1)
I2C1_SDA_ESP_IO10: J11.3, J12.3, RP2.2, U2.39 (17_A3_TX4_SDA1)
I2C_SCL: J5.7, J10.13, RP2.4, U2.41 (19_A5_SCL)
I2C_SDA: J5.8, J10.14, RP2.3, U2.40 (18_A4_SDA)
I2S2IN_GPIO5: J10.6, U2.7 (5_IN2)
I2S2MCLK_GPIO33: J12.15, U2.25 (33_MCLK2)
I2S2_OUT_GPIO2: J10.3, U2.4 (2_OUT2)
I2S_BCLK: J5.3, R8.1
I2S_DATAIN: J5.6, U2.10 (8_TX2_IN1)
I2S_DATAOUT: J5.5, R1.1
I2S_LRCLK: J5.4, R9.1
I2S_MCLK: J5.2, R7.1
LED0_GPIO30: D11.1 (K), J12.18, J19.2, U2.22 (30_CRX3)
LED1_GPIO31: D12.1 (K), J12.19, J20.2, U2.23 (31_CTX3)
LED2_GPIO32: D13.1 (K), J12.20, J21.2, U2.24 (32_OUT1B)
LRCK2_GPIO3: J10.4, U2.5 (3_LRCLK2)
unnamed: C1.1, J13.SH (SHIELD), R88.2
unnamed: C94.1, D1.3 (COM), R92.2, R100.2, U1.3 (+)
unnamed: CON3.Ssw, R89.1
unnamed: D11.2 (A), J19.1, R95.1
unnamed: D12.2 (A), J20.1, R96.1
unnamed: D13.2 (A), J21.1, R97.1
unnamed: J13.A5 (CC1), R86.1
unnamed: J13.B5 (CC2), R87.1
unnamed: R1.2, U2.9 (7_RX2_OUT1A)
unnamed: R2.2, U2.13 (11_MOSI_CTX1)
unnamed: R6.1, U2.35 (13_SCK_LED)
unnamed: R7.2, U2.45 (23_A9_CRX1_MCLK1)
unnamed: R8.2, U2.43 (21_A7_RX5_BCLK1)
unnamed: R9.2, U2.42 (20_A6_TX5_LRCLK1)
unnamed: R93.2, RV2.1, U1.4 (-)
unnamed: R94.1, RV2.2, RV2.3, U1.1
unnamed: RP1.1, TP1.1
OUT1A_MISO1_GPIO39: J12.9, U2.31 (39_MISO1_OUT1A)
PROG_BTN: SW4.1, U2.53 (PROGRAM)
RX1: J3.4, U2.2 (0_RX1_CRX2_CS1)
RX7_GPIO28: J12.16, U2.20 (28_RX7)
RX8_GPIO34_ADCCLIP: J12.14, JP10.2 (B), U2.26 (34_RX8)
SPI_CS_GPIO10: J10.9, U2.12 (10_CS_MQSR)
SPI_MISO_GPIO12: J10.11, U2.14 (12_MISO_MQSL)
SPI_MOSI_GPIO11: J10.10, R2.1
SPI_SCK_GPIO13: J10.12, R6.2
TX1: J3.3, U2.3 (1_TX1_CTX2_MISO1)
TX8_GPIO35: J12.13, U2.27 (35_TX8)
USB_H_D_N: J1.2 (D-), U2.56 (D-)
USB_H_D_P: J1.3 (D+), U2.57 (D+)
USB_H_PWR: J1.1 (VBUS), U2.55 (5V)
USB_N: J4.2, J13.A7 (D-), J13.B7 (D-)
USB_P: J4.3, J13.A6 (D+), J13.B6 (D+)
VEXP: C96.1, D1.2 (K), L6.1, R90.2, U1.5 (V+)
VPOT: C90.1, J16.1, J17.1, J18.1, L5.1

Notes on the sheet:
+5V Digital +5V Analog +8V Analog +3.3V - supplied by Teensy4.1
0 - UART RX1 (free) 1 - UART TX1 (free) 2 - I2S2 OUT (free) 3 - I2S2 LRCK2 (free) 4 - I2S2 BCK2 (free) 5 - I2S2 IN (free) 6 - OUT, Wet Control 7 - I2S OUT 8 - I2S IN 9 - OUT, DRY Control 10 - SPI CS (free) 11 - SPI MOSI (free) 12 - SPI MISO (free) 13 - SPI SCK (free)
14 - EXP PEDAL Sense 15 - EXP PEDAL Signal 16 - I2C1 SCL (ESP32) 17 - I2C1 SDA (ESP32) 18 - I2C SDA 19 - I2C SCL 20 - I2S LRCLK 21 - I2S BCK 22 - GUI INT (ESP32) 23 - I2S MCLK 24 - IN, FTSW0 25 - IN, FTSW1 26 - IN, FTSW2 27 - A13, POT Input
Do not use the MCP6001R version! (reversed power pins)
Input buffers Differntial drivers Signal presence detector Clip detector
Leds have two mounting options: - 0603 SMT - THT plug in using SMT pin sockets
Optional GPIO26 (Footswitch) or GPIO36
FPC 20 pin RM1.0mm LCSC suitable parts: C18198051
28 - RX7 (free) 29 - ADC+DAC PowerDown/Rst 30 - OUT, LED0 31 - OUT, LED1 32 - OUT, LED2 33 - I2S2 MCLK (Free) 34 - Optional ADC clip indicator 35 - (free) 36 - (free) Optional ESP IO13 37 - (free) 38 - (free) 39 - (free) 40 - A16, POT Input 41 - A17, POT Input
RV2 - EXP pedal range adjust gain to cover 0V-3.3V voltage range
1. Move the expression pedal to the top (toe) position. 2. Measure the voltage at ADC_EXP (pin 2 of J2). 3. Adjust the gain till the voltage reaches 3.3V DC. 4. Check if the full movement range (heel to toe) corresponds to the 0-3.3V voltage tange.
Momentary type SPST
Differntial receiver Dry/Wet mixer Volume control Output buffers
For Hammond 1590XX enclosure required standoff length = 29.5mm Use 29mm + one M3 washer
POT INPUTS
Calibration procedure:
TEENSY4.1
GPIO MAP
USB HOST
I2C PULL-UPS
EXPRESSION PEDAL INPUT
LEDS
EXT IO
ESP32S3 + DISPLAY
8MB PSRAM CHIP REQUIRED
UART1
USB DEVICE
EXT CODEC MODULE
FOOTSWITCH INPUTS
