hexeguitar/TGX4/firmware/TGX4_TeensyMainBoard/src/hardware_defs/hardware_defs.h

#ifndef _HARDWARE_DEFS_H_
#define _HARDWARE_DEFS_H_


// The USE_xxxxx flags creating the hw class are defined in the platformio.ini file
// by choosing the build environment.

// list of all avaialble hardware platforms
#include "hw_hexefx_tgx4.h"
#include "hw_hexefx_t40gfx.h"
#include "hw_hexefx_t41gfx.h"
#include "hw_teensy_audioBoard.h"
#include "hw_blackaddr_tgapro.h"
#include "hw_t40_ES8388.h"
#include "ctrl_WT32SC01Plus.h"
// add yours here:
// #include "hw_mycustomplatform.h"


#endif // _HARDWARE_DEFS_H_
