hexeguitar/TGX4/firmware/TGX4_TeensyMainBoard/src/RTNeural_models.cpp

/**
 * @file RTNeural_models.cpp
 * @author Piotr Zapart www.hexefx.com
 * @brief Based on Seed pedal design by
 * 		 Keith Bloemer (GuitarML) https://github.com/GuitarML/Seed
 * 		Ported to Teensy4.1 with the following additions/changes:
 * 			- adjusted model volume to match unity gain with bypass signal
 * 			- dual mono input and output
 * 			- added bypass system
 * @version 0.1
 * @date 2024-01-31
 */
#include "RTNeural_models.h"

modelData Model1; 
modelData Model2; 
modelData Model3;
modelData Model4; 
modelData Model5; 
modelData Model6; 
modelData Model7;
modelData Model8; 

modelData Model9;


std::vector<modelData> model_collection;

void setupWeights() {

// COPY AND PASTE YOUR MODEL WEIGHTS BELOW (After converting .json to .h file) ////////////////////////////////// < -------------------
//   ADD AND REMOVE MODELS AS DESIRED (CAN HOLD AROUND 15-16 MODELS IN FLASH MEMORY)

//../newNeuralSeedModel fender57_g5_gru9_p003_shift16 maybe keep
/*
model : SimpleRNN
input_size : 1
skip : 1
output_size : 1
unit_type : GRU
num_layers : 1
hidden_size : 9
bias_fl : True
*/

  Model1.rec_weight_ih_l0 = {{0.010945625603199005, -0.050199560821056366, -0.06624435633420944, -0.1976807862520218, 0.1158326119184494, -0.06330181658267975, -0.0030009972397238016, 0.010331690311431885, 0.04662841558456421, 0.050783343613147736, -0.14239542186260223, -0.146307110786438, -0.0151847954839468, 0.025679081678390503, -0.1442670226097107, 0.06651495397090912, 0.1271495223045349, 0.13272543251514435, -0.43817561864852905, -1.1551047563552856, -0.03793826326727867, 0.8241645097732544, 0.842648446559906, 0.8103972673416138, -0.01621781662106514, -1.3673923015594482, 0.8390907645225525}}; 

  Model1.rec_weight_hh_l0 = {{0.2660585641860962, -0.06399577111005783, 0.1198706179857254, 0.11052851378917694, 0.20094873011112213, -0.2052612602710724, -0.21146216988563538, -0.12754301726818085, 0.32190588116645813, 0.14035136997699738, -0.07555074989795685, 0.21440546214580536, 0.41187435388565063, 0.0024969112128019333, 0.29178300499916077, 0.24995334446430206, -0.2648366689682007, -0.3174993395805359, 0.9455024600028992, 0.5280759334564209, -0.06975415349006653, -0.5438200235366821, 0.3096756339073181, -0.07702699303627014, 0.7434556484222412, -0.7418537735939026, 0.2919408679008484}, 
                            { 0.20359723269939423, -0.0020075237844139338, 0.07313552498817444, 0.08402300626039505, 0.04145404323935509, -0.1683993637561798, 0.06027502194046974, -0.1064407229423523, 0.17345184087753296, 0.28747838735580444, 0.1693194955587387, -0.003262239508330822, 0.12429770827293396, 0.17810338735580444, 0.2705853283405304, -0.17416897416114807, 0.06282186508178711, 0.08296966552734375, 0.09632748365402222, 0.331215500831604, -0.8628224730491638, -1.292256474494934, 0.016151534393429756, 0.11461299657821655, 0.07012607902288437, -0.5104307532310486, 0.19750377535820007}, 
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

  Model8.levelAdjust = 0.55;


  // ADD YOUR MODEL IDENTIFIER HERE ////////////////////////////////// < -------------------------
  model_collection = {  Model1, Model5, Model2, Model6, Model3, Model7, Model4, Model8};
}
