hexeguitar/TGX4/firmware/TGX4_TeensyMainBoard/src/system.cpp

#include "system.h"

// PSRAM speed by KurtE
// https://forum.pjrc.com/index.php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
// added PSRAM presence check P.Z. 12.2024

extern uint8_t external_psram_size;

bool update_psram_speed(int speed_mhz)
{
	if (external_psram_size == 0) return false;
	// What clocks exist:
	static const int flexspio2_clock_speeds[] = {396, 720, 665, 528};

	// See what the closest setting might be:
	uint8_t clk_save, divider_save;
	int min_delta = speed_mhz;
	for (uint8_t clk = 0; clk < 4; clk++)
	{
		uint8_t divider = (flexspio2_clock_speeds[clk] + (speed_mhz / 2)) / speed_mhz;
		int delta = abs(speed_mhz - flexspio2_clock_speeds[clk] / divider);
		if ((delta < min_delta) && (divider < 8))
		{
			min_delta = delta;
			clk_save = clk;
			divider_save = divider;
		}
		else return false;
	}

	// first turn off FLEXSPI2
	CCM_CCGR7 &= ~CCM_CCGR7_FLEXSPI2(CCM_CCGR_ON);

	divider_save--; // 0 based.
	// Serial.printf("Update FLEXSPI2 speed: %u clk:%u div:%u Actual:%u\n", speed_mhz, clk_save, divider_save,
	// 			  flexspio2_clock_speeds[clk_save] / (divider_save + 1));

	// Set the clock settings.
	CCM_CBCMR = (CCM_CBCMR & ~(CCM_CBCMR_FLEXSPI2_PODF_MASK | CCM_CBCMR_FLEXSPI2_CLK_SEL_MASK)) | CCM_CBCMR_FLEXSPI2_PODF(divider_save) | CCM_CBCMR_FLEXSPI2_CLK_SEL(clk_save);

	// Turn FlexSPI2 clock back on
	CCM_CCGR7 |= CCM_CCGR7_FLEXSPI2(CCM_CCGR_ON);
	return true;
}
