hexeguitar/TGX4/firmware/TGX4_WT32SC01PLUS_GUI/src/display.h

#ifndef _DISPLAY_H_
#define _DISPLAY_H_

#include <Arduino.h>
#define LGFX_USE_V1
#include <LovyanGFX.hpp>
#include <lvgl.h>

class LGFX : public lgfx::LGFX_Device
{
	lgfx::Panel_ST7796 _panel_instance;
	lgfx::Bus_Parallel8 _bus_instance;
	lgfx::Light_PWM _light_instance;
	lgfx::Touch_FT5x06 _touch_instance;

public:
	LGFX(void)
	{
		{
			auto cfg = _bus_instance.config();
			cfg.freq_write = 40000000;
			cfg.pin_wr = 47;
			cfg.pin_rd = -1;
			cfg.pin_rs = 0;
			cfg.pin_d0 = 9;
			cfg.pin_d1 = 46;
			cfg.pin_d2 = 3;
			cfg.pin_d3 = 8;
			cfg.pin_d4 = 18;
			cfg.pin_d5 = 17;
			cfg.pin_d6 = 16;
			cfg.pin_d7 = 15;
			_bus_instance.config(cfg);
			_panel_instance.setBus(&_bus_instance);
		}
		{
			auto cfg = _panel_instance.config();
			cfg.pin_cs = -1;
			cfg.pin_rst = 4;
			cfg.pin_busy = -1;
			cfg.memory_width = 320;
			cfg.memory_height = 480;
			cfg.panel_width = 320;
			cfg.panel_height = 480;
			cfg.offset_x = 0;
			cfg.offset_y = 0;
			cfg.offset_rotation = 0;
			cfg.dummy_read_pixel = 8;
			cfg.dummy_read_bits = 1;
			cfg.readable = true;
			cfg.invert = true;
			cfg.rgb_order = false;
			cfg.dlen_16bit = false;
			cfg.bus_shared = false;

			_panel_instance.config(cfg);
		}
		{
			auto cfg = _light_instance.config();
			cfg.pin_bl = 45;
			cfg.invert = false;
			cfg.freq = 44100;
			cfg.pwm_channel = 7;

			_light_instance.config(cfg);
			_panel_instance.setLight(&_light_instance);
		}
		{
			auto cfg = _touch_instance.config();
			cfg.i2c_port = 1;
			cfg.i2c_addr = 0x38;
			cfg.pin_sda = 6;
			cfg.pin_scl = 5;
			cfg.pin_int = 7;
			cfg.freq = 400000;
			cfg.x_min = 0;
			cfg.x_max = 320;
			cfg.y_min = 0;
			cfg.y_max = 480;

			_touch_instance.config(cfg);
			_panel_instance.setTouch(&_touch_instance);
		}
		setPanel(&_panel_instance);
	}
};

void display_init();

#endif // _DISPLAY_H_
